robbertvdzon/schaakrob/3dmodellen/v2/hoekpunten/stappenmotorhouder_linksboven.scad

mirror(v= [1,0,0] ) {
    include <stappenmotorhouder_linksonder.scad>;
}
