robbertvdzon/schaakrob/3dmodellen/v2/hoekpunten/stappenmotorhouder_rechtsboven.scad

mirror(v= [1,0,0] ) {
    mirror(v= [0,1,0] ) {
        include <stappenmotorhouder_linksonder.scad>;
    }
}
