robbertvdzon/schaakrob/3dmodellen/v2/hoekpunten/stappenmotorhouder_rechtsonder.scad

mirror(v= [0,1,0] ) {
  include <stappenmotorhouder_linksonder.scad>;
}
