robbertvdzon/schaakrob/3dmodellen/v2/schaakstukken/dame2d.scad

          import(file = "svg/dame_dicht.svg", layer = "plate");
          
