robbertvdzon/schaakrob/3dmodellen/v2/schaakstukken/pion-dun.scad

difference(){
	union(){ 

        difference(){
            union(){ 
                translate([-27.5, -2,0]){
                    linear_extrude(height = 0.3, center = false, convexity = 10)
                    scale([1,1]) import(file = "svg/pion_dicht.svg", layer = "plate");
                }                              
            }
            union() {
               
            }
         }

	}
	union() {
    }
}


 
