robbertvdzon/schaakrob/3dmodellen/v2/schaakstukken/pion2d.scad

          import(file = "svg/pion_dicht.svg", layer = "plate");
          
