robbertvdzon/schaakrob/3dmodellen/v2/schakelaar/schakelaar-horizontaal-boven.scad

mirror(v= [0,1,0] ) {
  include <schakelaar-horizontaal.scad>;
}
