robbertvdzon/schaakrob/arduino/pakker24ghz-sender/pakker24ghz-sender.ino

/*

---
i2c protocol:
byte 0 : altijd ^
byte 1 : command
byte 2 : not used
byte 3 : not used
byte 4 : not used
byte 5 : not used
byte 6 : not used
byte 7 : not used

states:
0: initial
1: ready
2: grabbing
3: releaseing

*/

#include <Wire.h>
#include <RF24.h> // see https://github.com/tmrh20/RF24/

#define NR_OF_BYTES_TO_READ 12
#define READY 1
#define GRABBING 2
#define RELEASING 3
#define beepPin 9
#define WAIT_TIME_AFTER_GRAB 700
#define WAIT_TIME_AFTER_RELEASE 400


char command;
char number[50];
int state = READY;
int readPos = 0;
int SLAVE_ADDRESS = 5;

RF24 radio(7, 8); // CE, CSN
const byte address[6] = "00002";

void setup() {

  pinMode(beepPin, OUTPUT);

  Serial.begin(9600);
  Serial.println("Starting pakkersender");
  Serial.print("Slave on adress:");
  Serial.println(SLAVE_ADDRESS);

  Wire.begin(SLAVE_ADDRESS);
  Wire.onReceive(receiveData);
  Wire.onRequest(sendData);

  bootSeq();

  digitalWrite(beepPin, LOW);

  if (!radio.begin()) {
    Serial.println(F("radio hardware is not responding!!"));
    errorSeq();
    while (1) {} // hold in infinite loop
  }
  radio.openWritingPipe(address);

  radio.setChannel(108); // channel with less noise
  radio.setPALevel(RF24_PA_LOW);
  radio.setDataRate(RF24_250KBPS);
  radio.setCRCLength(RF24_CRC_8);
  radio.setPayloadSize(sizeof("pak1"));
  radio.stopListening();
  Serial.println("radio ready");
}

void loop() {
  processCommand();
}

void sendData(){
   Wire.write(state);
}

void receiveData(int byteCount){
  while(Wire.available()) {
    processCharRead(Wire.read());
  }
}

void processCharRead(char c){
  if (c == '^'){
    readPos = 0;
  }

  if (readPos < NR_OF_BYTES_TO_READ){
    number[readPos] = c;
    number[readPos+1] = '\0';
  }

  readPos ++;
  if (readPos == NR_OF_BYTES_TO_READ){
    parseCommand();
  }
}


void parseCommand(){
  Serial.print("parseCommand:");
  Serial.println(number);
  command = number[1];

  Serial.print("- cmd:");Serial.println(command);
}

void processCommand(){
 if (command == 'C') clamp1();
 if (command == 'R') release1();
 if (command == 'W') clamp2();
 if (command == 'E') release2();
}

void clamp1(){
  state = GRABBING;
  Serial.println("grabbing arm 1");
  const char text[] = "pak1";
  bool result = sendWithRetry(&text, sizeof(text));
  if (result){
    Serial.println("grabbed");
  }
  else{
    Serial.println("grabbing failed");
  }
  delay(WAIT_TIME_AFTER_GRAB); // return ready after grab is finished (performed by the reciever)
  state = READY;
  command = '-';
}

void release1(){
  state = RELEASING;
  Serial.println("releasing arm 1");
  const char text[] = "zet1";
  bool result = sendWithRetry(&text, sizeof(text));
  if (result){
    Serial.println("released");
  }
  else{
    Serial.println("releasing failed");
  }
  delay(WAIT_TIME_AFTER_RELEASE); // return ready after release is finished (performed by the reciever)
  state = READY;
  command = '-';
}

void clamp2(){
  state = GRABBING;
  Serial.println("grabbing arm 2");
  const char text[] = "pak2";
  bool result = sendWithRetry(&text, sizeof(text));
  if (result){
    Serial.println("grabbed");
  }
  else{
    Serial.println("grabbing failed");
  }
  delay(WAIT_TIME_AFTER_GRAB); // return ready after grab is finished (performed by the reciever)
  state = READY;
  command = '-';
}

void release2(){
  state = RELEASING;

  Serial.println("releasing arm 2");
  const char text[] = "zet2";
  bool result = sendWithRetry(&text, sizeof(text));
  if (result){
    Serial.println("released");
  }
  else{
    Serial.println("releasing failed");
  }
  delay(WAIT_TIME_AFTER_RELEASE); // return ready after release is finished (performed by the reciever)
  state = READY;
  command = '-';
}

bool sendWithRetry(const void* buf, uint8_t len){
  int retryCount = 0;
  int MAX_RETRIES = 300; // max 30 seconds
  bool succeeded = radio.write(buf, len);
  while (retryCount<MAX_RETRIES && !succeeded){
    retryCount++;
    delay(100);
    Serial.print("failed, try again:");
    Serial.println(retryCount);
    succeeded = radio.write(buf, len); // try again
  }
  return succeeded;
}

void bootSeq(){
  beep();
  beep();
  command = '-';
}

void errorSeq(){
  beep();
  delay(500);
  beep();
  delay(500);
  beep();
  delay(500);
  beep();
  delay(500);
  beep();
  command = '-';
}


void beep(){
    digitalWrite(beepPin, HIGH);
    delay(100);
    digitalWrite(beepPin, LOW);
    delay(100);
}
